osiweb/unified_retro_keyboard/documents/Photo Jul 10, 12 20 41 PM.jpg

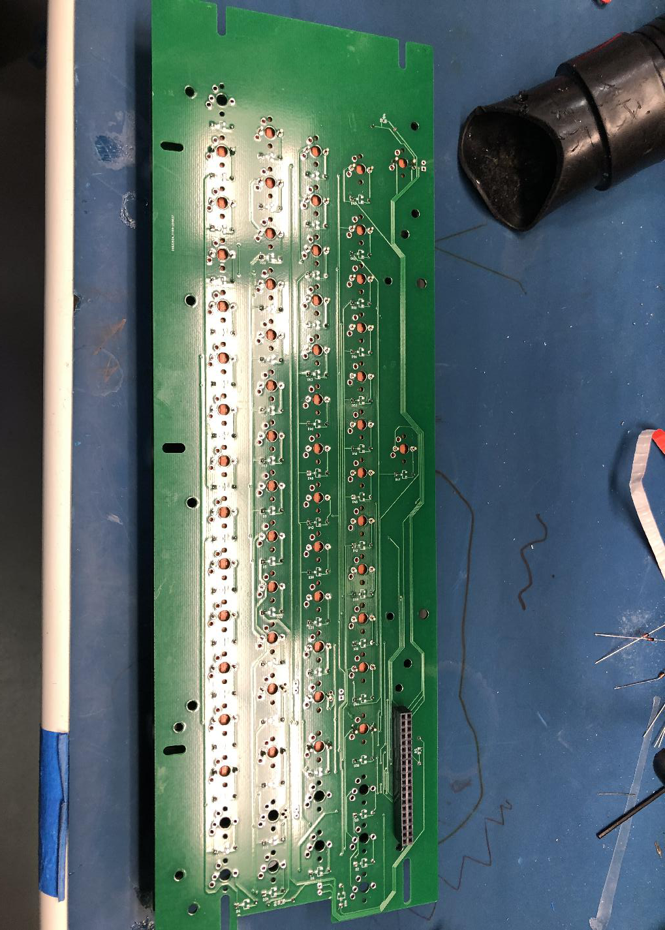
documents/Photo Jul 10, 12 20 41 PM.jpg
