osiweb/unified_retro_keyboard/documents/build-images/futaba_posts_installed_on_spacebar.jpg

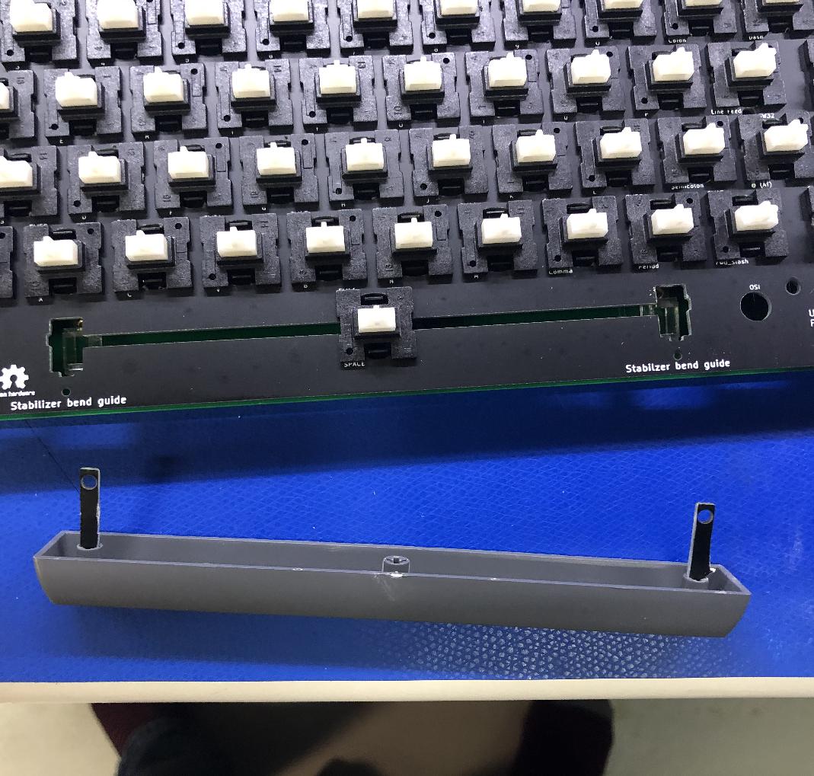
documents/build-images/futaba_posts_installed_on_spacebar.jpg
