osiweb/unified_retro_keyboard/documents/build-images/posts_removed.jpg

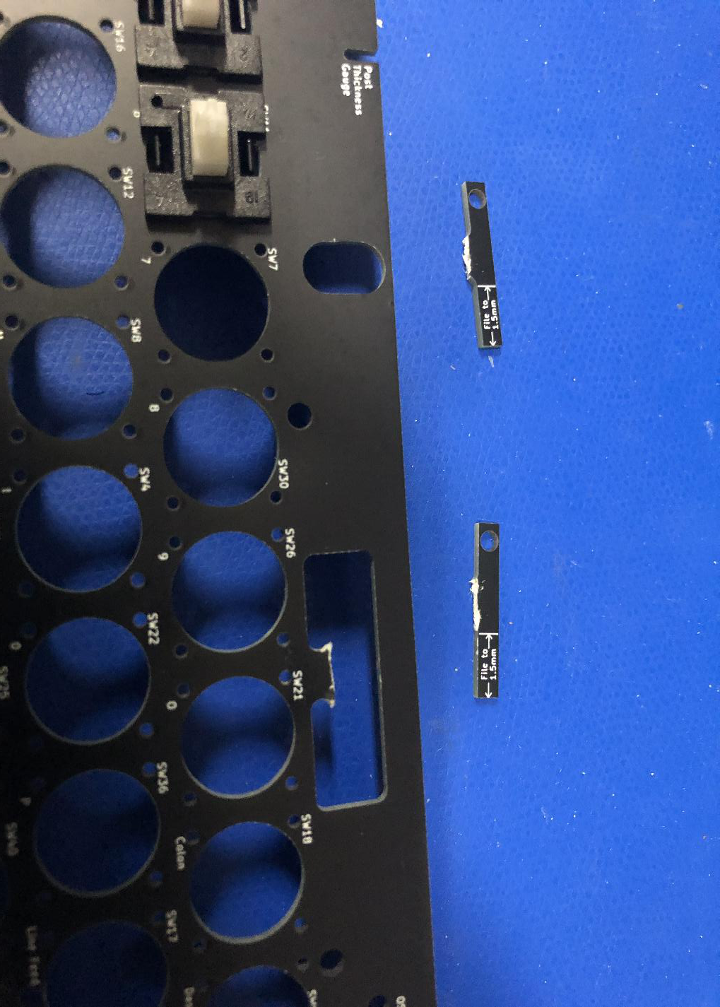
documents/build-images/posts_removed.jpg
