osiweb/unified_retro_keyboard/documents/build-images/stabilizer_rod_stock.jpg

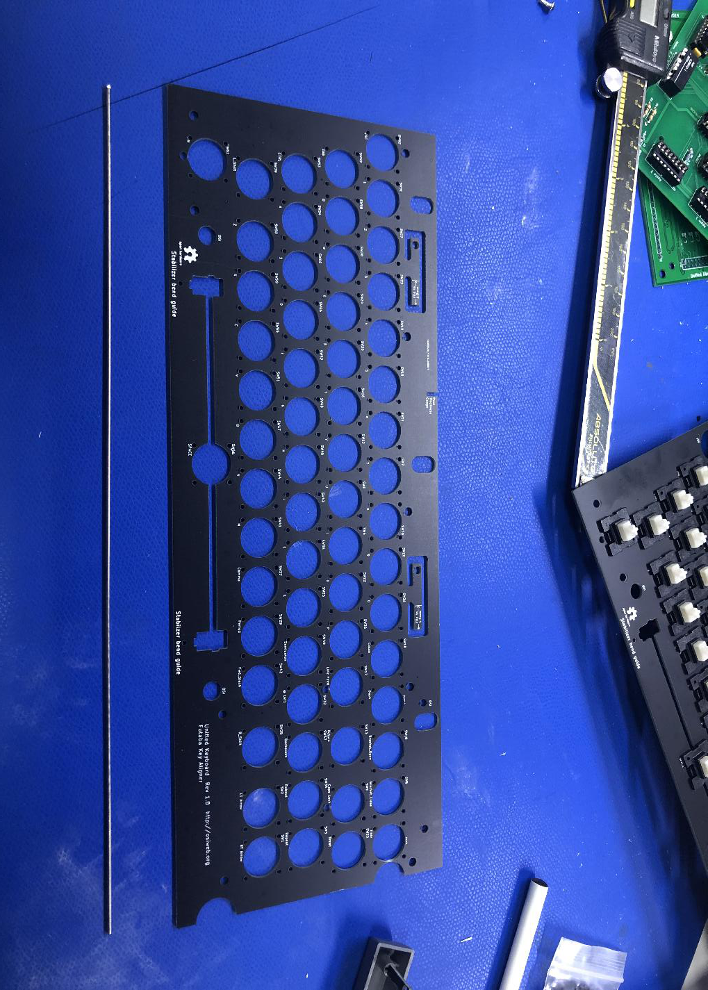
documents/build-images/stabilizer_rod_stock.jpg
