osiweb/unified_retro_keyboard/documents/build-images/Tape Diodes_in_place.jpg

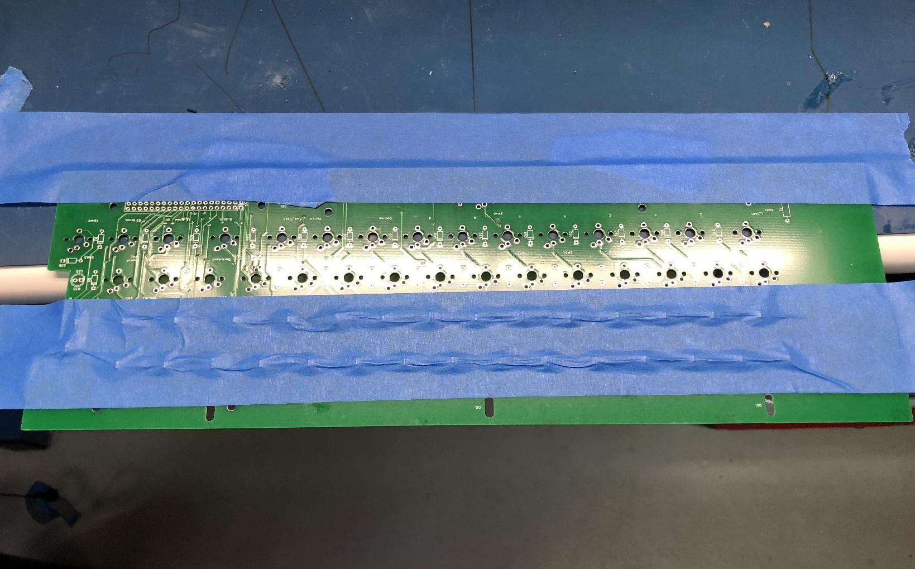
documents/build-images/Tape Diodes_in_place.jpg
